CatalinSerafimescu/CapacitorDischarger/simulation/results/C_mid_100V_100uF/out.csv

 1.00000000e-05  9.84049926e+01  1.00000000e-05  1.76412485e-02  1.00000000e-05  3.52824970e-02  1.00000000e-05  9.83949992e-03  1.00000000e-05  1.94940425e+00  1.00000000e-05  9.92022507e+01  1.00000000e-05 -7.97258079e-01  1.00000000e-05  4.18744650e-03  1.00000000e-05  9.61839221e-11  1.00000000e-05  2.20936001e-04  1.00000000e-05  1.96790306e-04  1.00000000e-05  2.50000000e+01  1.00000000e-05  0.00000000e+00
 1.02820767e-05  9.84049787e+01  1.02820767e-05  1.81329329e-02  1.02820767e-05  3.55638091e-02  1.02820767e-05  9.83949853e-03  1.02820767e-05  1.94790947e+00  1.02820767e-05  9.92022368e+01  1.02820767e-05 -7.97258099e-01  1.02820767e-05  4.18744590e-03  1.02820767e-05  9.61836039e-11  1.02820767e-05  2.20939702e-04  1.02820767e-05  1.96790278e-04  1.02820767e-05  2.50000000e+01  1.02820767e-05  0.00000000e+00
 1.08462302e-05  9.84049511e+01  1.08462302e-05  1.91081089e-02  1.08462302e-05  3.62485347e-02  1.08462302e-05  9.83949576e-03  1.08462302e-05  1.94790945e+00  1.08462302e-05  9.92022092e+01  1.08462302e-05 -7.97258062e-01  1.08462302e-05  4.18744473e-03  1.08462302e-05  9.61831033e-11  1.08462302e-05  2.20939633e-04  1.08462302e-05  1.96790223e-04  1.08462302e-05  2.50000000e+01  1.08462302e-05  0.00000000e+00
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
 2.69545212e-01  8.60347444e+01  2.69545212e-01  7.83795252e-02  2.69545212e-01  7.83797690e-02  2.69545212e-01  8.60260084e-03  2.69545212e-01  1.93996420e+00  2.69545212e-01  8.68249828e+01  2.69545212e-01 -7.90238308e-01  2.69545212e-01  3.66105296e-03  2.69545212e-01  8.40940808e-11  2.69545212e-01  1.90049359e-04  2.69545212e-01  1.72052284e-04  2.69545212e-01  2.50000000e+01  2.69545212e-01  0.00000000e+00
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
