CatalinSerafimescu/CapacitorDischarger/simulation/results/D_low_50V_100uF/out.csv

 1.00000000e-05  4.84792793e+01  1.00000000e-05  1.03251343e-02  1.00000000e-05  2.06502686e-02  1.00000000e-05  4.84743585e-03  1.00000000e-05  1.90487976e+00  1.00000000e-05  4.92395193e+01  1.00000000e-05 -7.60239980e-01  1.00000000e-05  2.06294806e-03  1.00000000e-05  4.73894636e-11  1.00000000e-05  9.63166716e-05  1.00000000e-05  9.69488637e-05  1.00000000e-05  2.50000000e+01  1.00000000e-05  0.00000000e+00
 1.02828661e-05  4.84792726e+01  1.02828661e-05  1.06169452e-02  1.02828661e-05  2.09331678e-02  1.02828661e-05  4.84743518e-03  1.02828661e-05  1.90433846e+00  1.02828661e-05  4.92395125e+01  1.02828661e-05 -7.60239933e-01  1.02828661e-05  2.06294777e-03  1.02828661e-05  4.73901054e-11  1.02828661e-05  9.63180066e-05  1.02828661e-05  9.69488503e-05  1.02828661e-05  2.50000000e+01  1.02828661e-05  0.00000000e+00
 1.08485982e-05  4.84792592e+01  1.08485982e-05  1.12000878e-02  1.08485982e-05  2.14993641e-02  1.08485982e-05  4.84743384e-03  1.08485982e-05  1.90433844e+00  1.08485982e-05  4.92394990e+01  1.08485982e-05 -7.60239837e-01  1.08485982e-05  2.06294720e-03  1.08485982e-05  4.73896079e-11  1.08485982e-05  9.63179732e-05  1.08485982e-05  9.69488235e-05  1.08485982e-05  2.50000000e+01  1.08485982e-05  0.00000000e+00
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
