CatalinSerafimescu/CapacitorDischarger/simulation/results/A_full_600V_1mF/plot.png

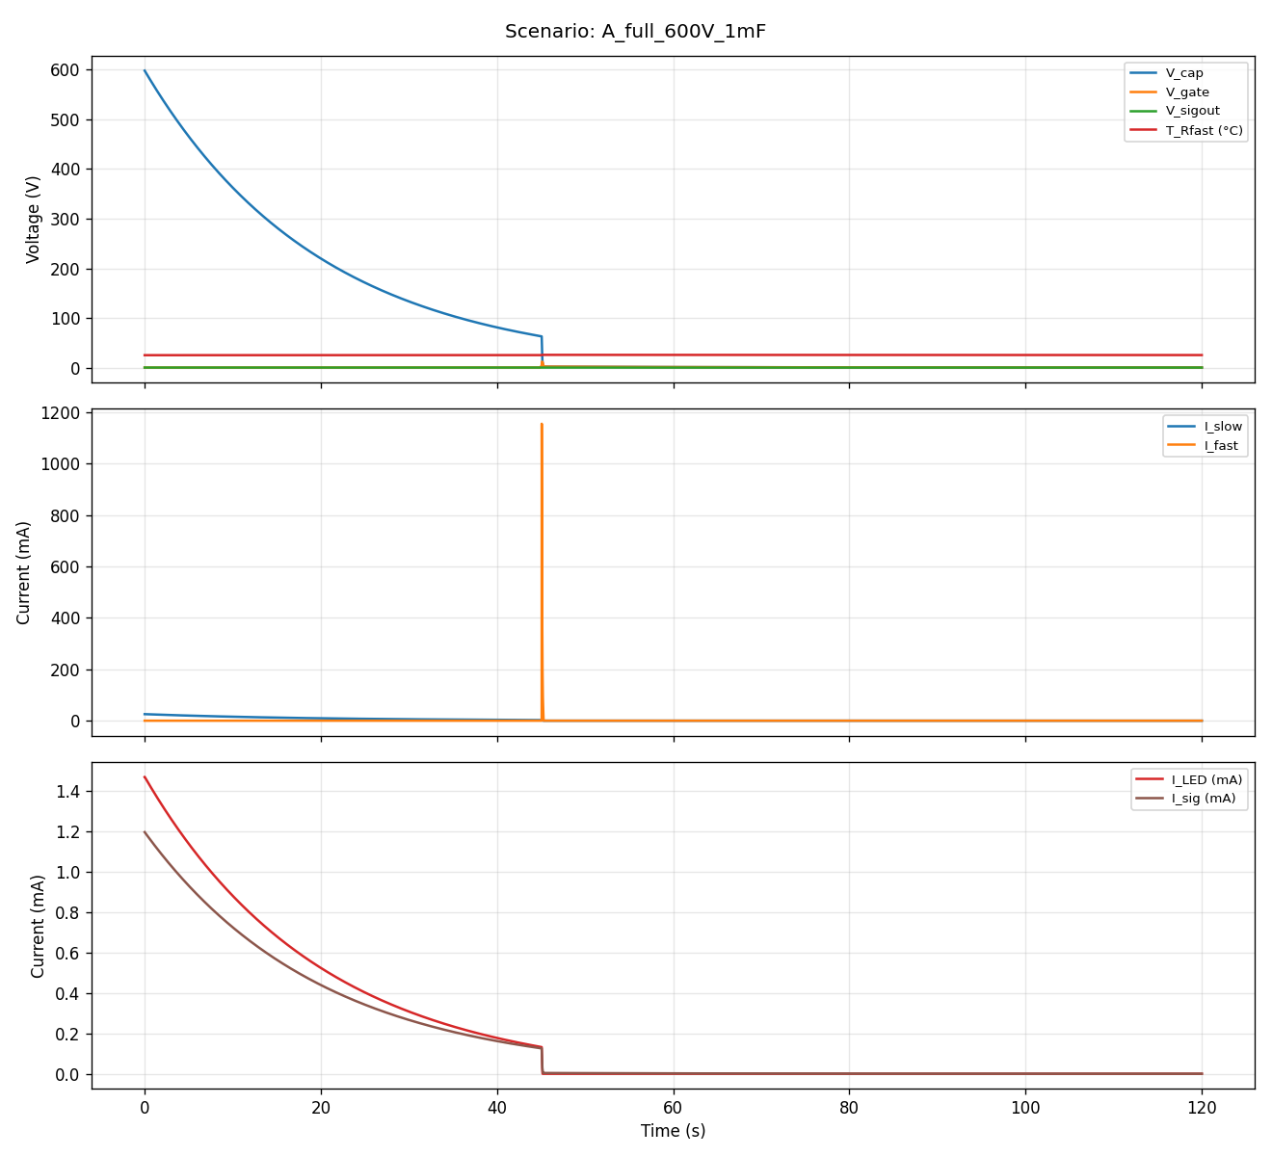
simulation/results/A_full_600V_1mF/plot.png
