CatalinSerafimescu/CapacitorDischarger/simulation/results/B_mid_300V_470uF/plot.png

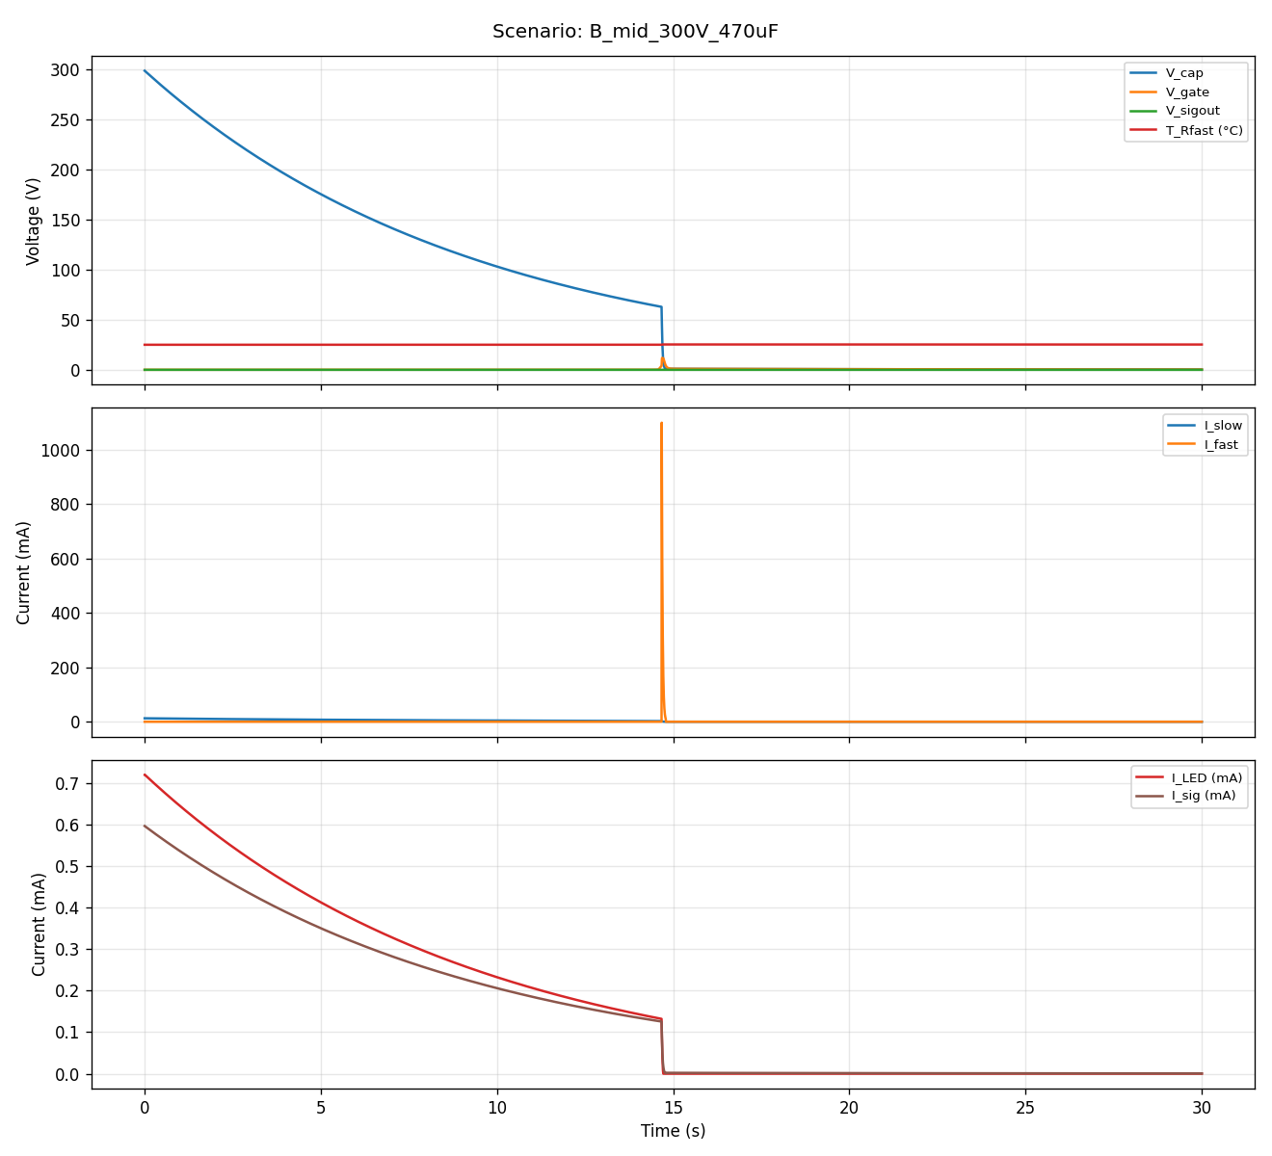
simulation/results/B_mid_300V_470uF/plot.png
