CatalinSerafimescu/CapacitorDischarger/simulation/results/C_mid_100V_100uF/plot.png

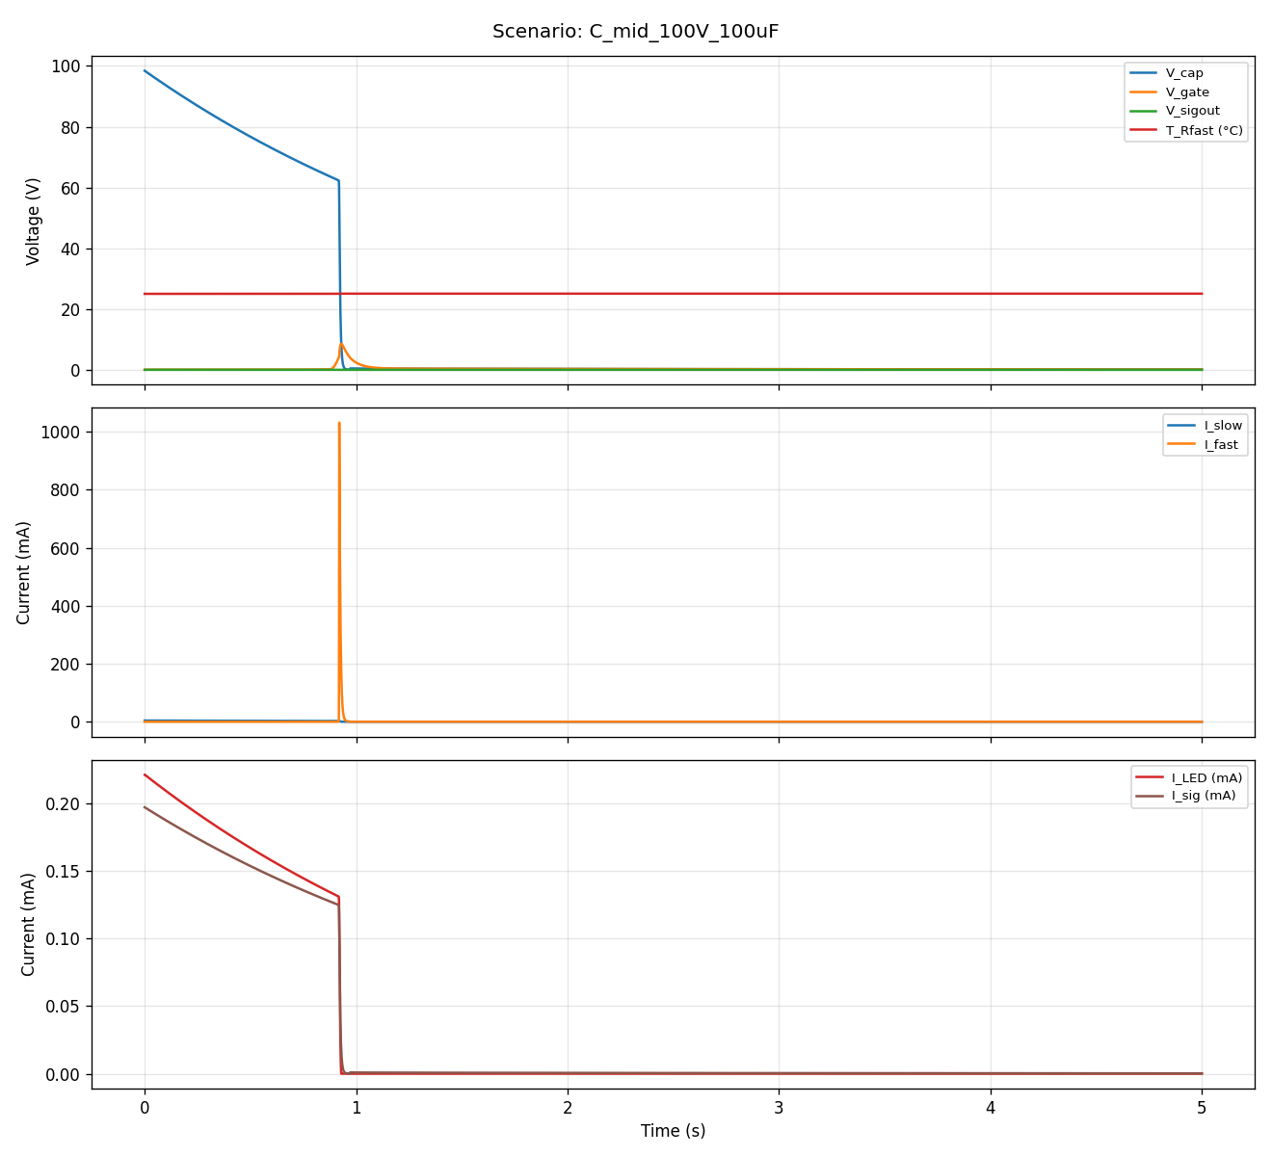
simulation/results/C_mid_100V_100uF/plot.png
