CatalinSerafimescu/CapacitorDischarger/simulation/results/D_low_50V_100uF/plot.png

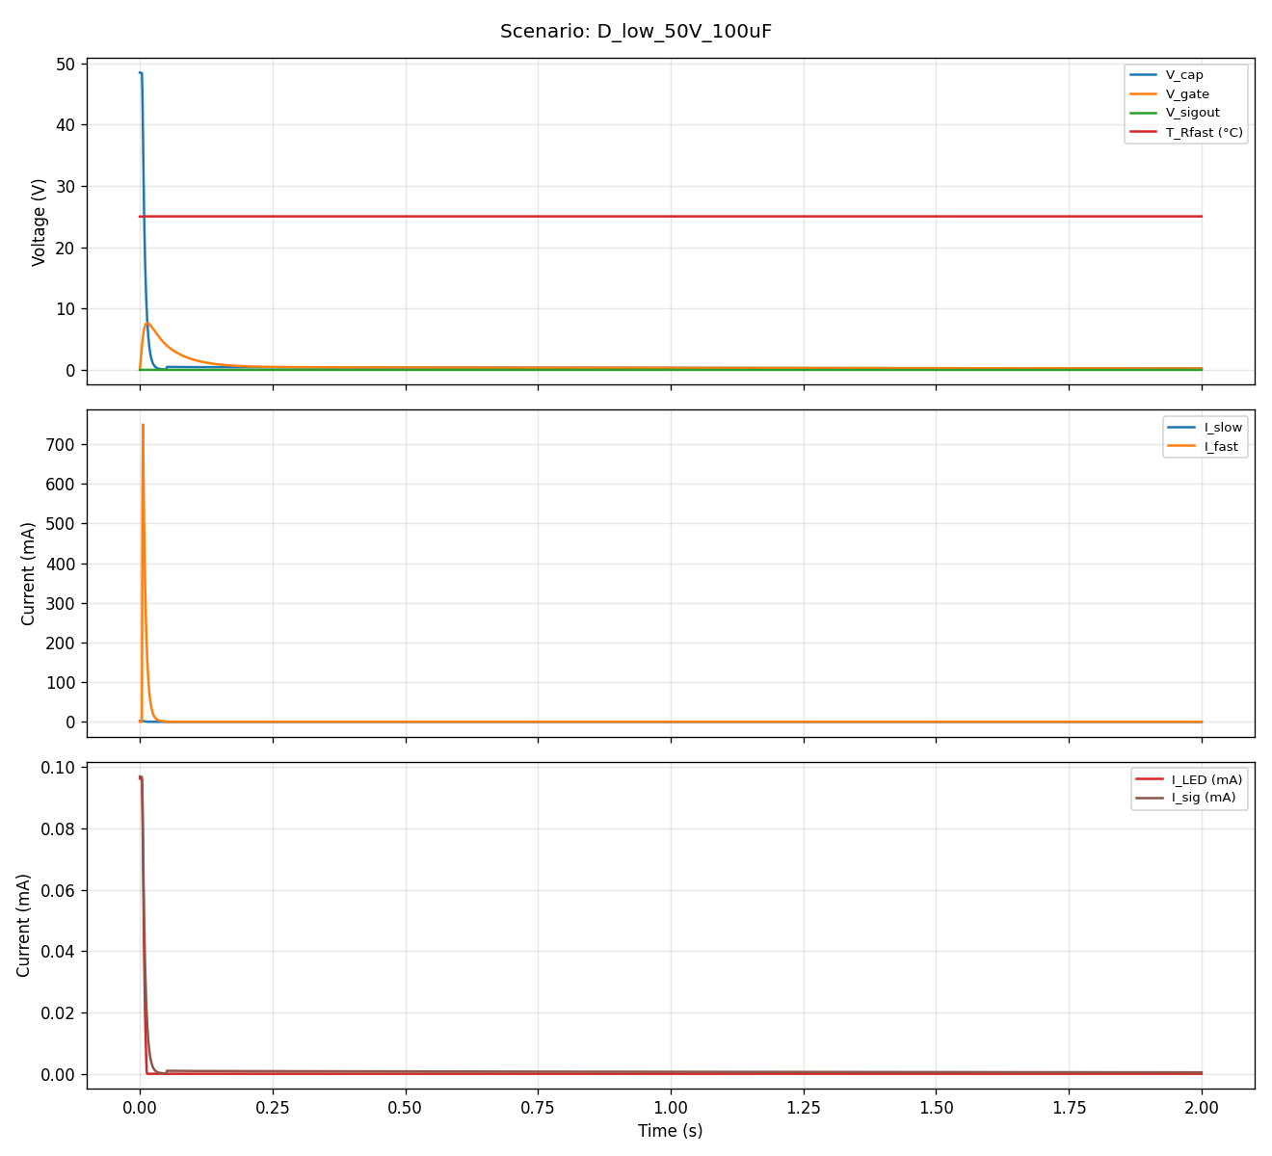
simulation/results/D_low_50V_100uF/plot.png
