CatalinSerafimescu/CapacitorDischarger/simulation/results/E_below_LED_8V_100uF/plot.png

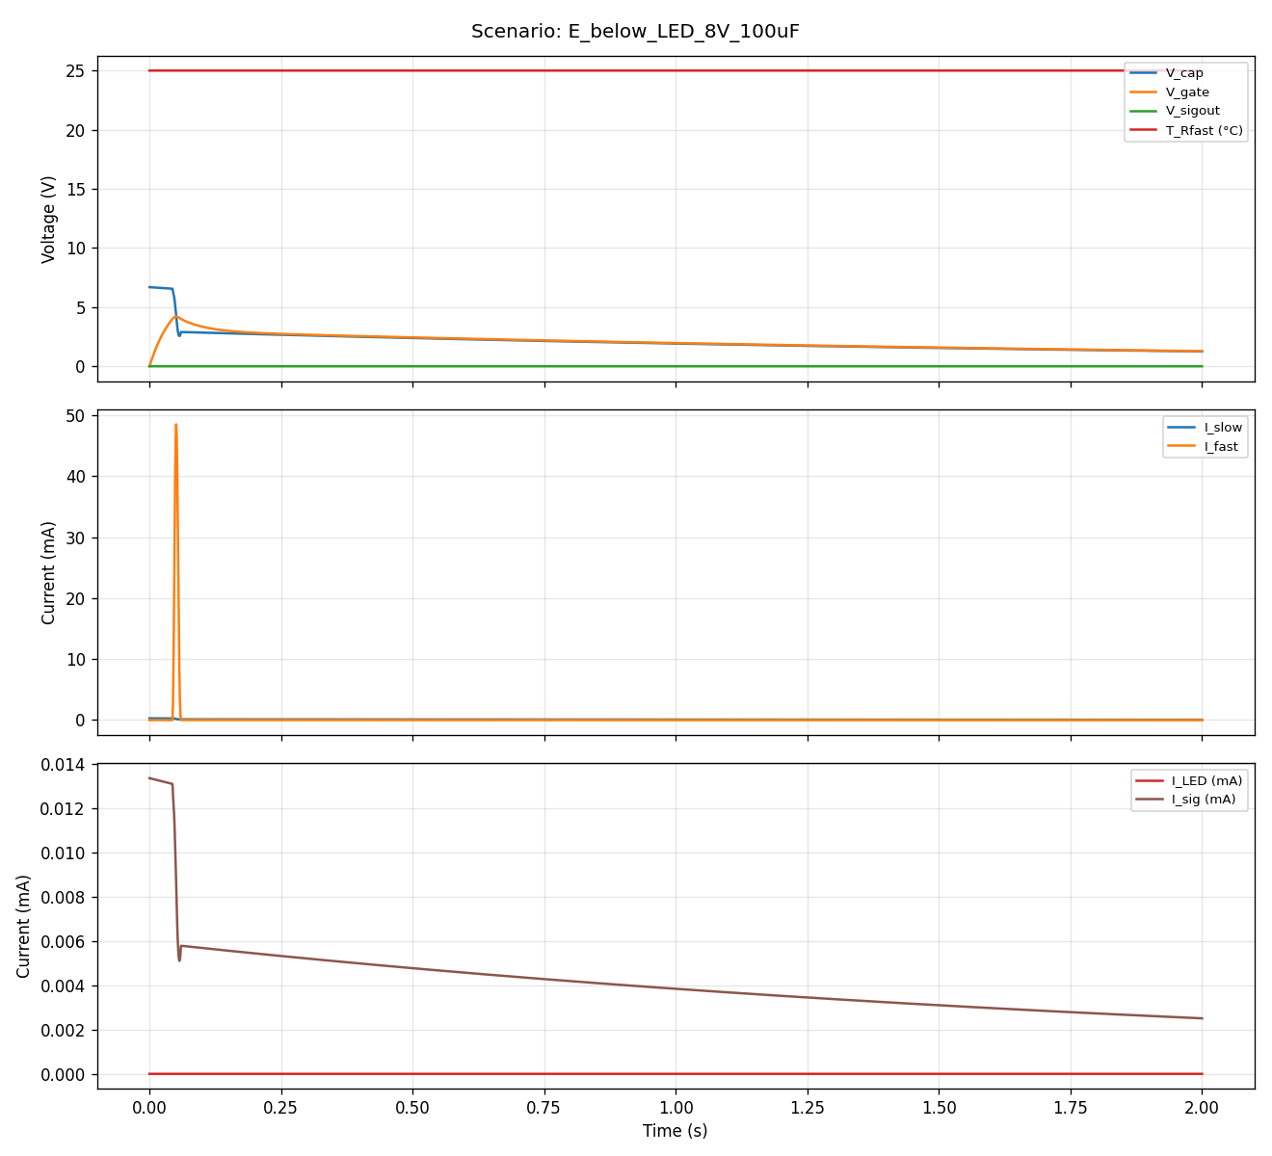
simulation/results/E_below_LED_8V_100uF/plot.png
