CatalinSerafimescu/CapacitorDischarger/simulation/results/F_steady_state_600V/plot.png

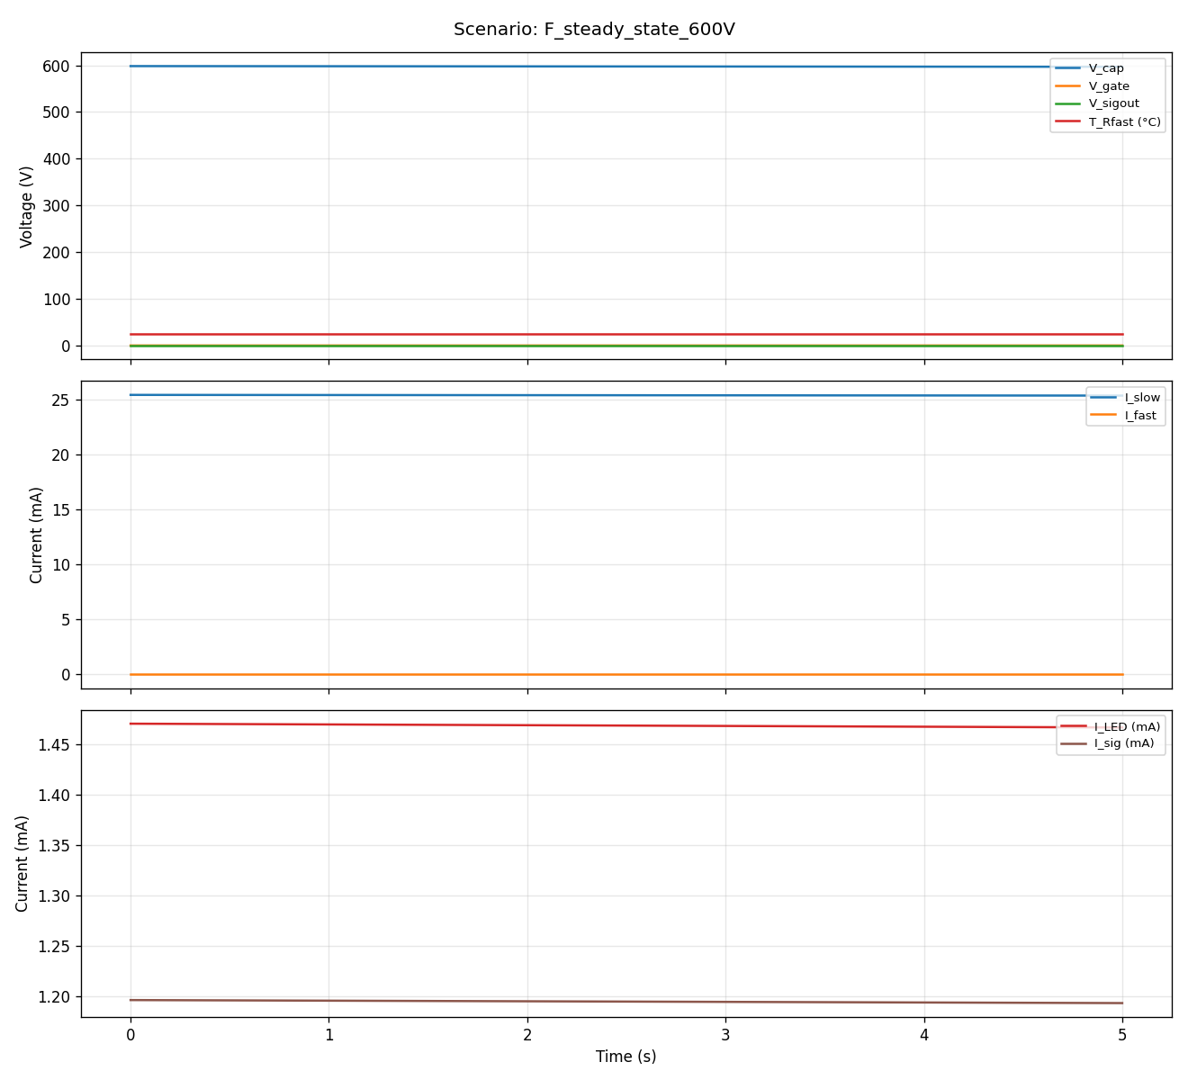
simulation/results/F_steady_state_600V/plot.png
