CatalinSerafimescu/CapacitorDischarger/simulation/results/G2_threshold_lowbeta/plot.png

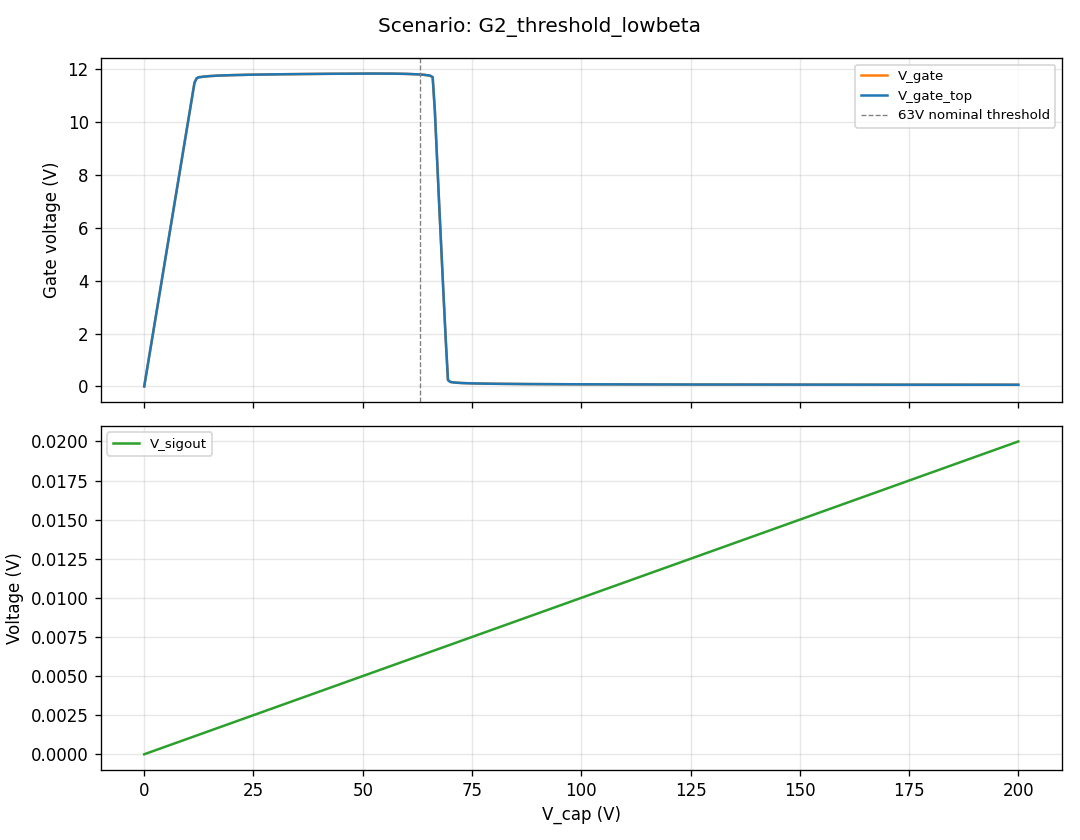
simulation/results/G2_threshold_lowbeta/plot.png
