CatalinSerafimescu/CapacitorDischarger/simulation/results/G3_threshold_cold_lowhfe/plot.png

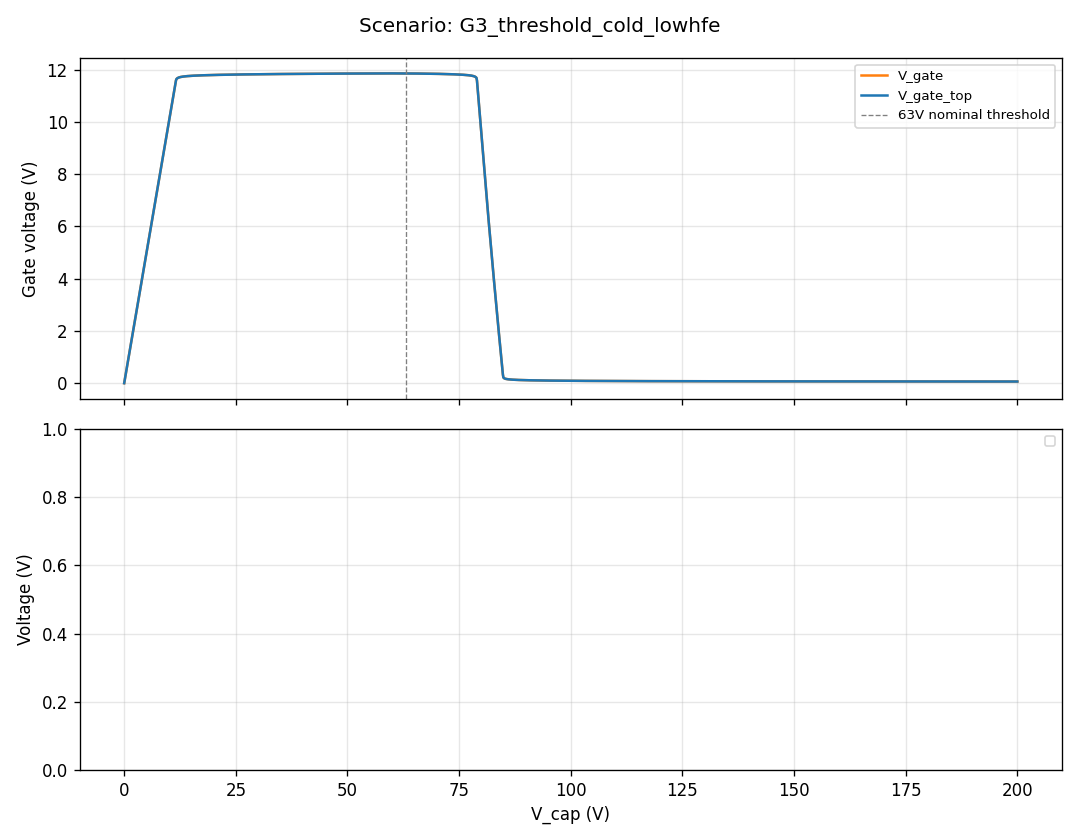
simulation/results/G3_threshold_cold_lowhfe/plot.png
