CatalinSerafimescu/CapacitorDischarger/simulation/results/G4_threshold_hot_highhfe/plot.png

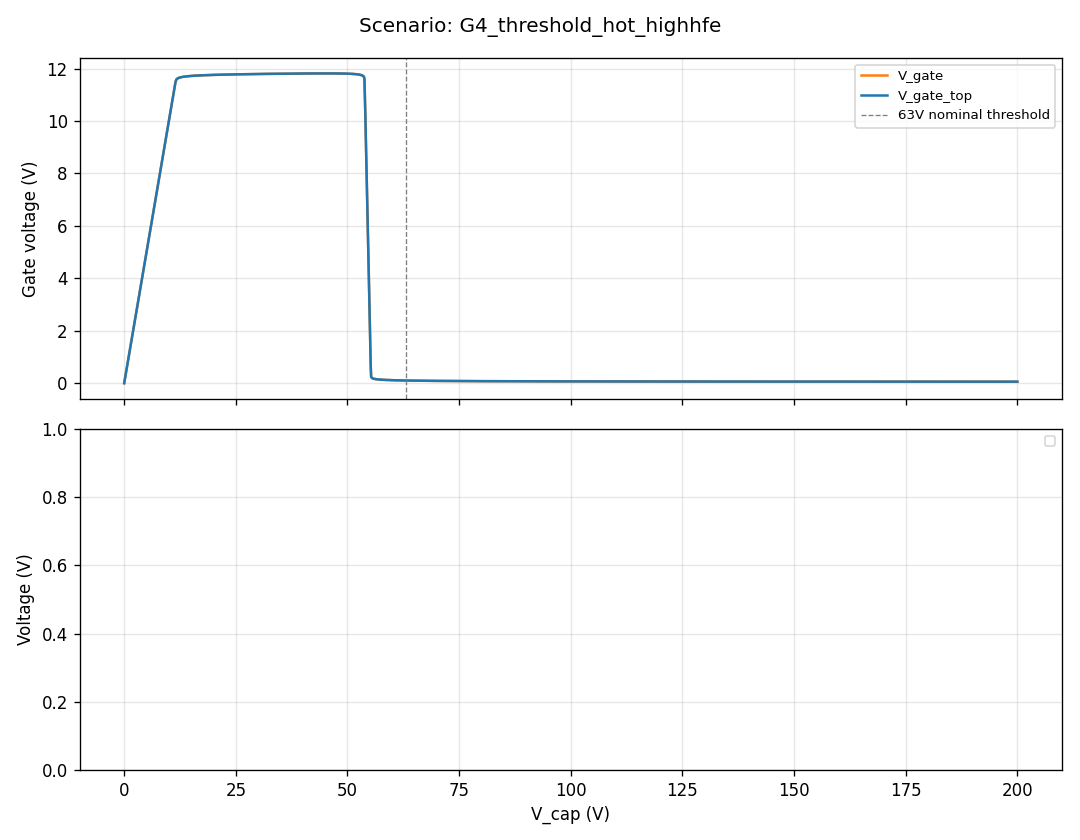
simulation/results/G4_threshold_hot_highhfe/plot.png
