CatalinSerafimescu/CapacitorDischarger/simulation/results/H_dvm_divider_clamp/plot.png

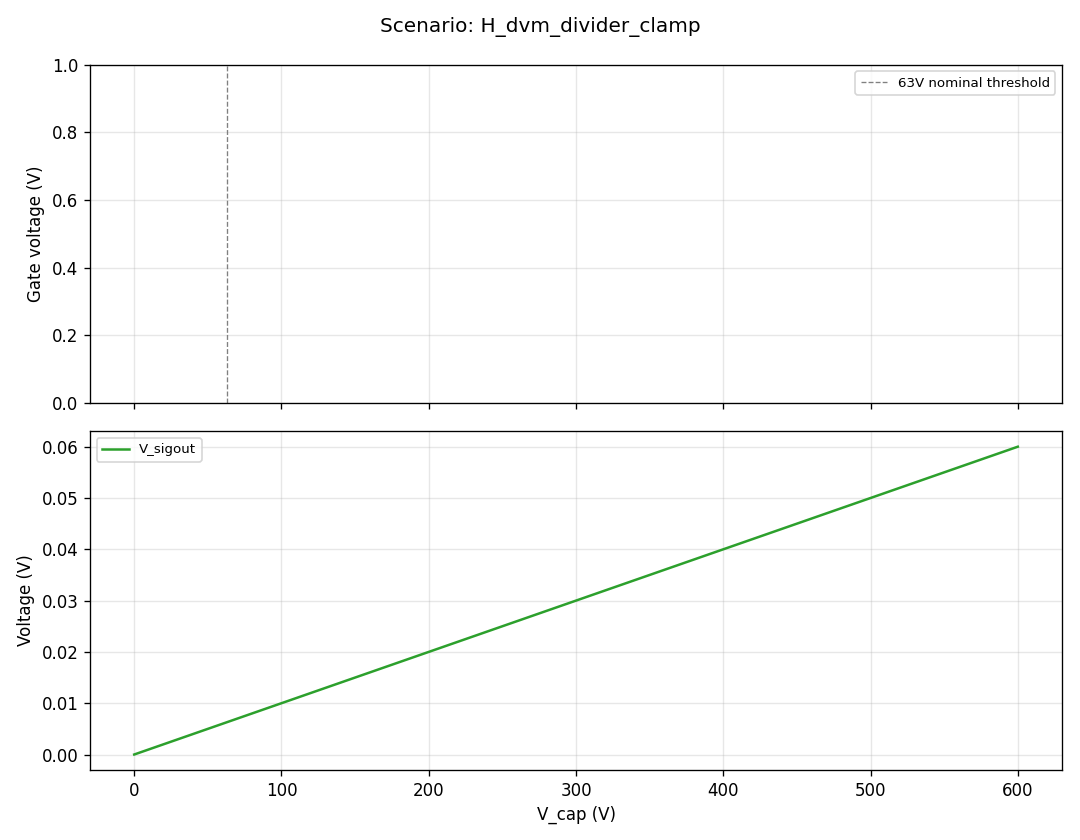
simulation/results/H_dvm_divider_clamp/plot.png
