CatalinSerafimescu/CapacitorDischarger/simulation/results/J_hotplug_600V/plot.png

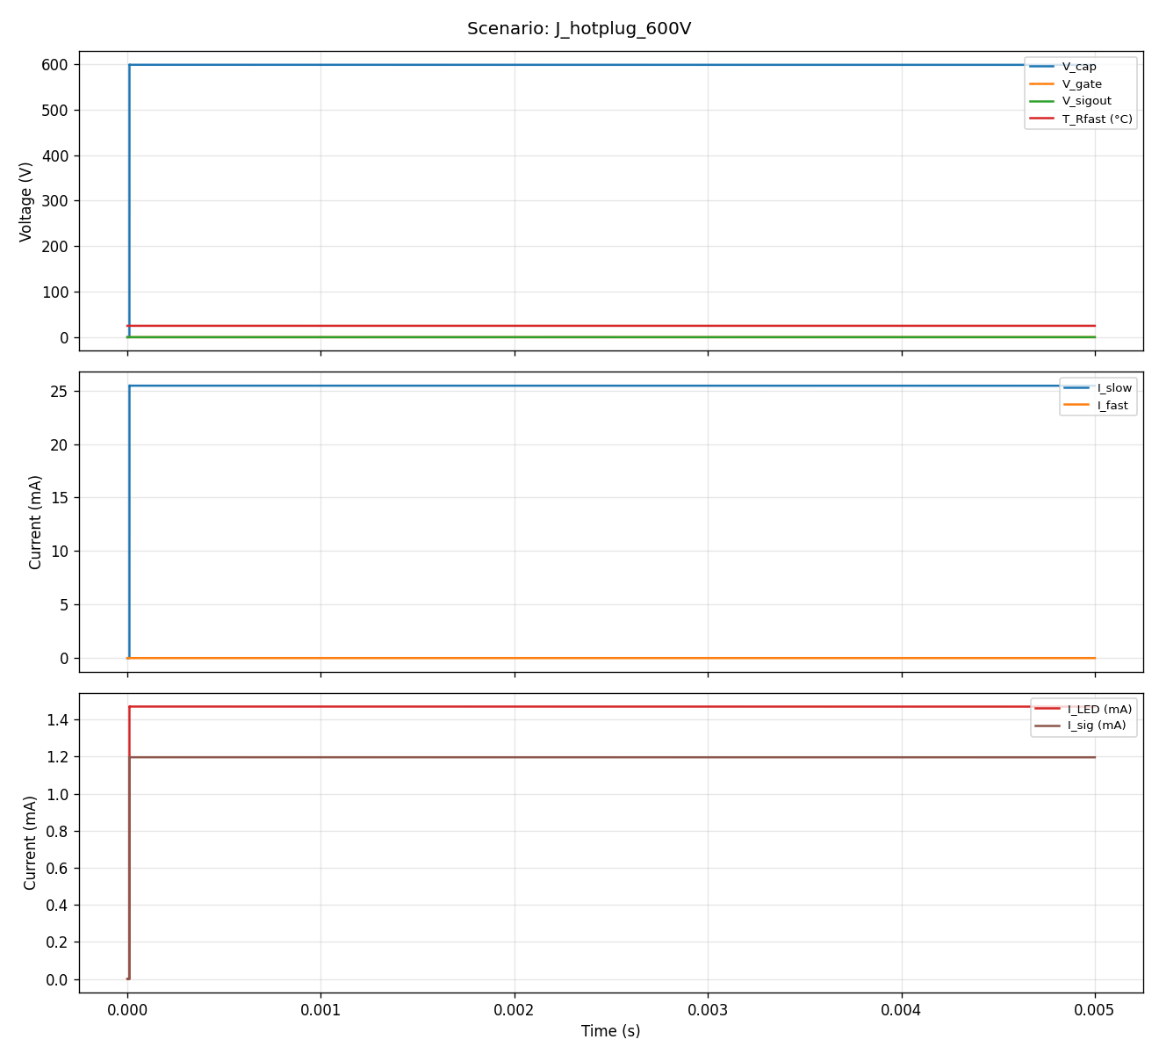
simulation/results/J_hotplug_600V/plot.png
