CatalinSerafimescu/CapacitorDischarger/simulation/results/K_bigcap_60V_47mF/plot.png

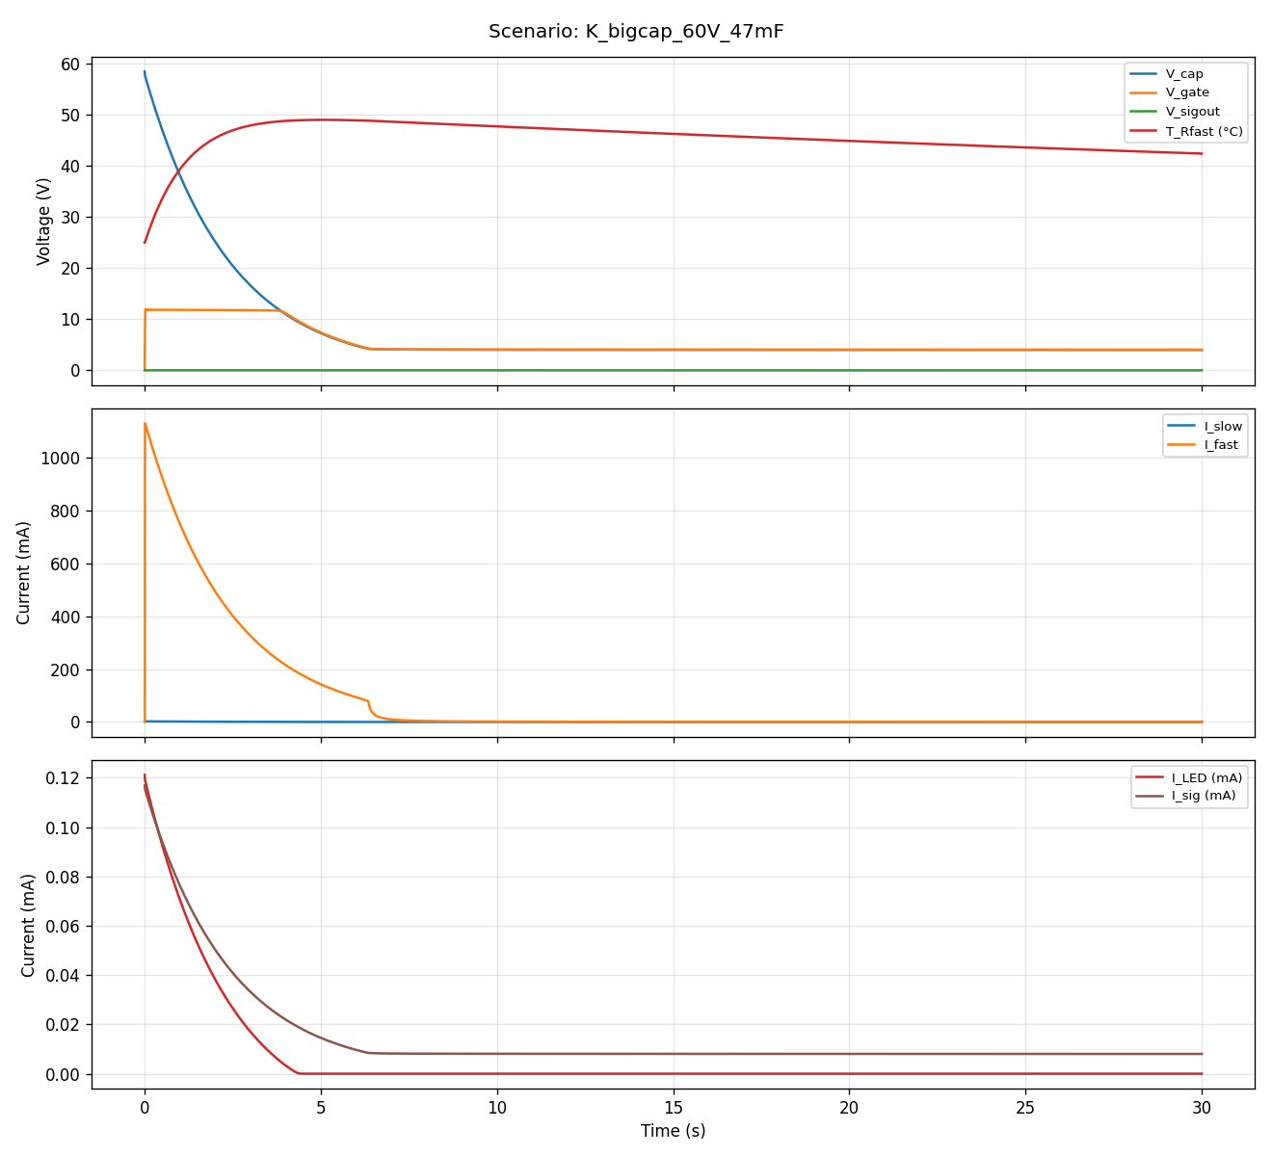
simulation/results/K_bigcap_60V_47mF/plot.png
