CatalinSerafimescu/CapacitorDischarger/simulation/results/L_live_supply_48V/plot.png

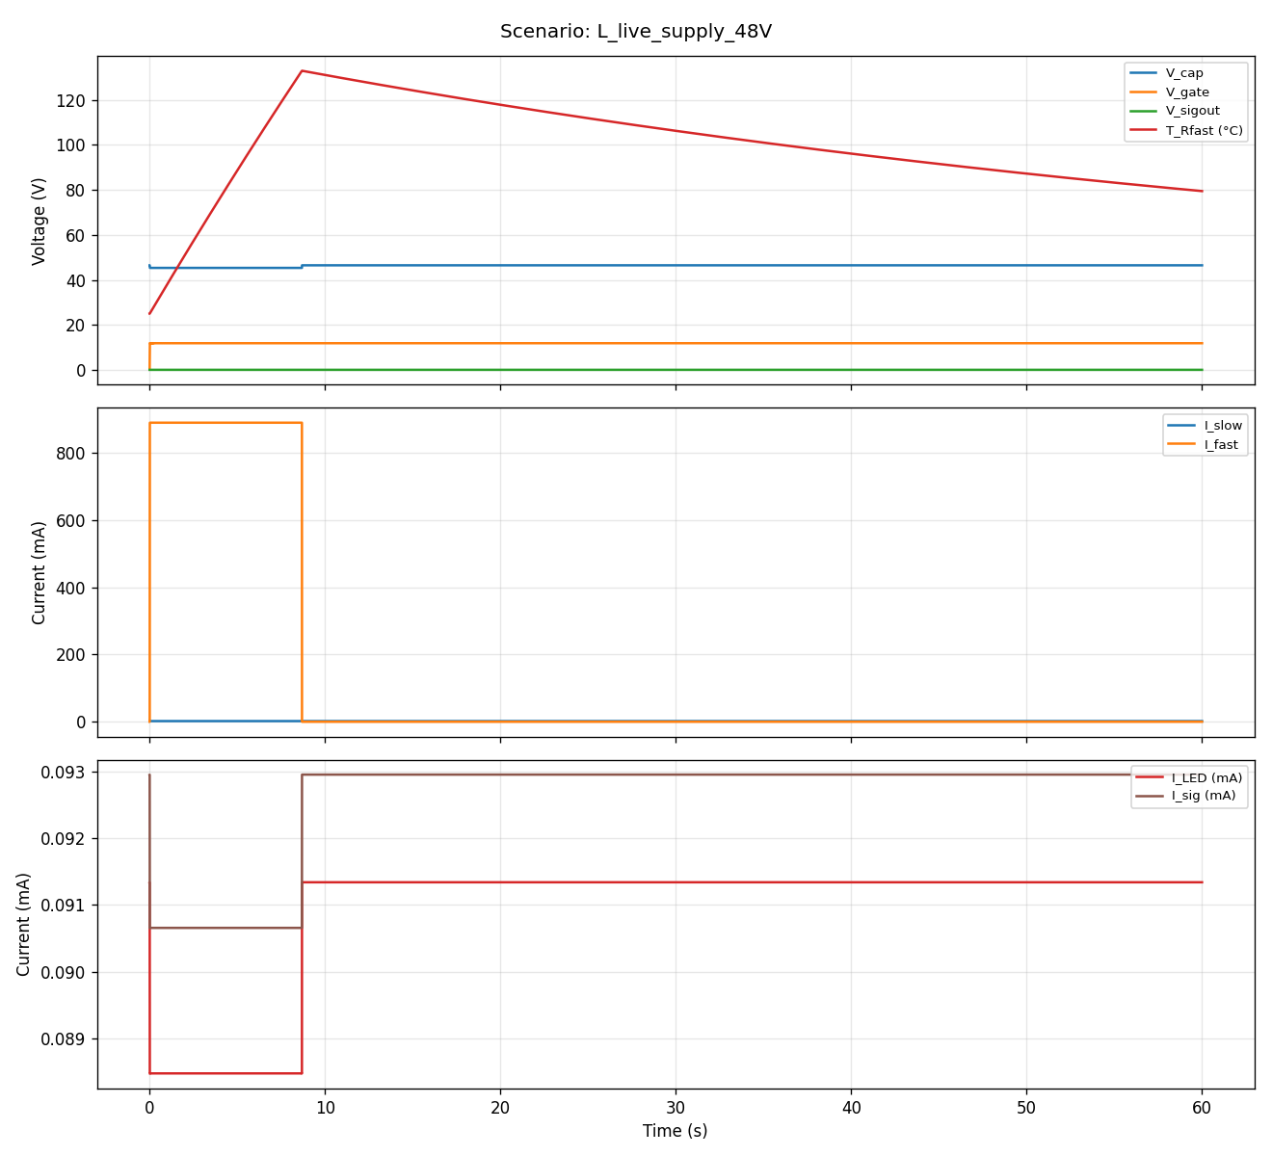
simulation/results/L_live_supply_48V/plot.png
